andregasser/swisscom-myai-desk-lamp/output/multicolor_v4/print/04_base_P1S.3mf

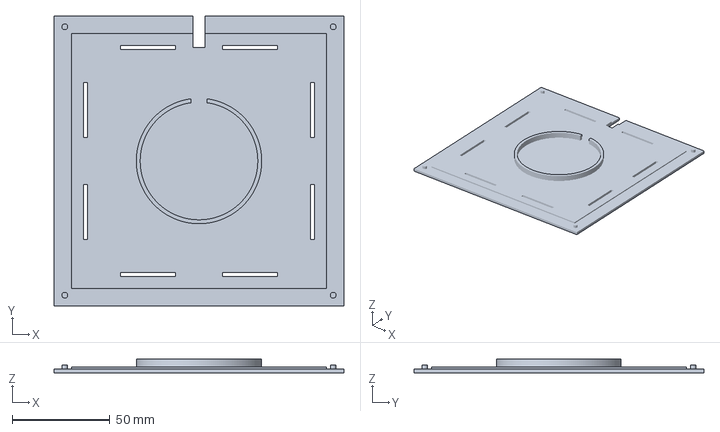
[picture p23: CAD file, 2026-09-30]
output/multicolor_v4/print/04_base_P1S.3mf
148.0 x 148.0 x 6.98 mm
