andregasser/swisscom-myai-desk-lamp/output/multicolor_v4/print/07_fit_P1S.3mf

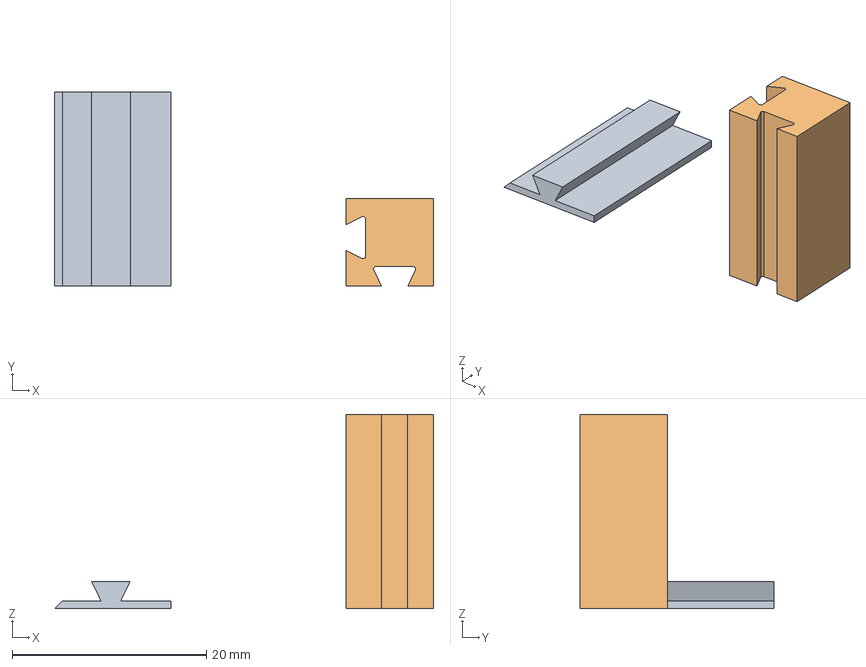
[picture p24: CAD file, 2026-09-30]
output/multicolor_v4/print/07_fit_P1S.3mf
39.0 x 20.0 x 20.0 mm
07_fit_panel
07_fit_corner
