andregasser/swisscom-myai-desk-lamp/output/multicolor_v4/stl/07_fit_corner.stl

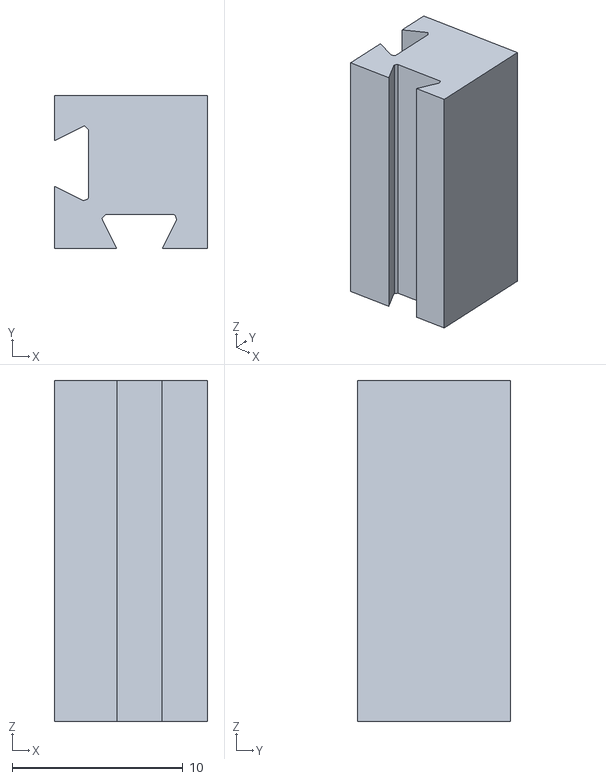
[picture p25: CAD file, 2026-09-30]
output/multicolor_v4/stl/07_fit_corner.stl
9.00 x 9.00 x 20.0
