andregasser/swisscom-myai-desk-lamp/output/stl/01f_joint_socket.stl

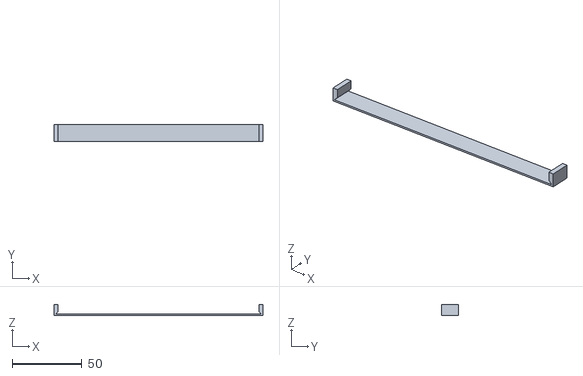
[picture p26: CAD file, 2026-09-28]
output/stl/01f_joint_socket.stl
150.0 x 12.0 x 8.00
