andregasser/swisscom-myai-desk-lamp/output/stl/01e_led_fit.stl

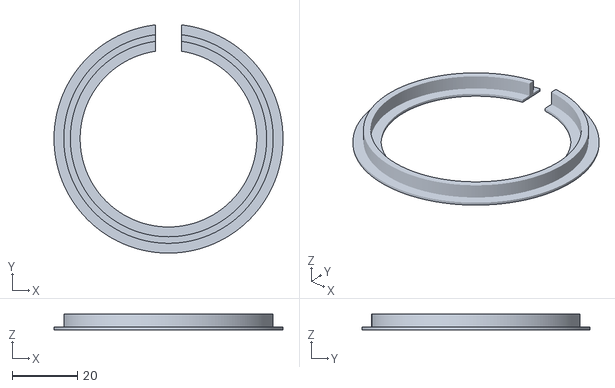
[picture p27: CAD file, 2026-09-28]
output/stl/01e_led_fit.stl
70.0 x 69.8 x 4.78
