andregasser/swisscom-myai-desk-lamp/output/stl/01g_joint_rail.stl

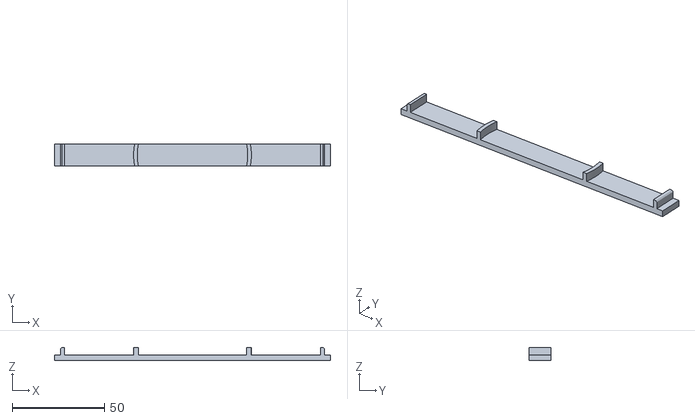
[picture p28: CAD file, 2026-09-28]
output/stl/01g_joint_rail.stl
150.0 x 12.0 x 7.00
