andregasser/swisscom-myai-desk-lamp/output/multicolor_v4/stl/02_panel_1_Weiss.stl

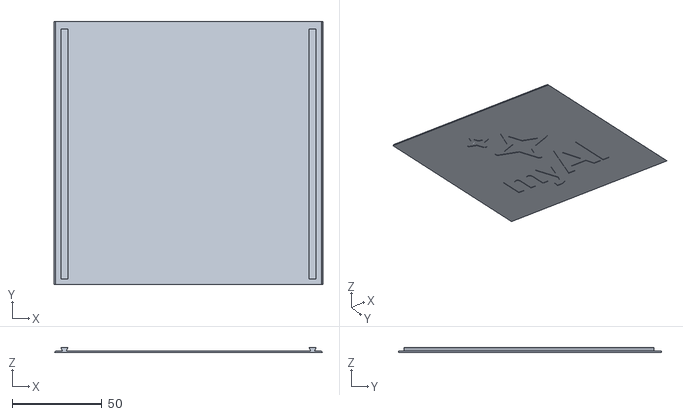
[picture p29: CAD file, 2026-09-30]
output/multicolor_v4/stl/02_panel_1_Weiss.stl
149.6 x 146.0 x 2.80
