andregasser/swisscom-myai-desk-lamp/output/stl/01d_light_1.2mm.stl

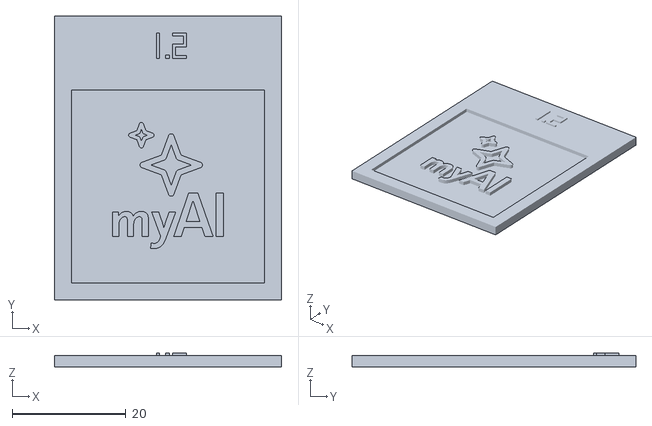
[picture p30: CAD file, 2026-09-28]
output/stl/01d_light_1.2mm.stl
40.0 x 50.0 x 2.38
