andregasser/swisscom-myai-desk-lamp/output/multicolor_v4/stl/02_panel_2_Blau.stl

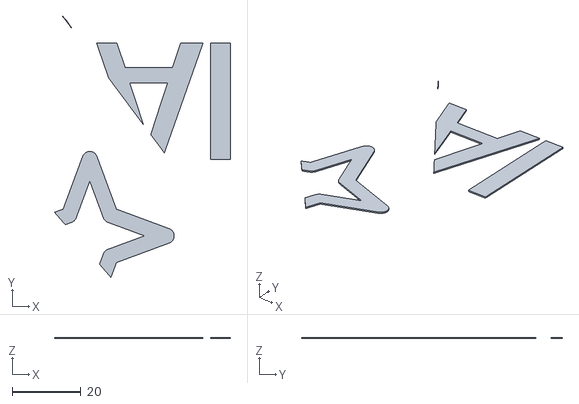
[picture p31: CAD file, 2026-09-30]
output/multicolor_v4/stl/02_panel_2_Blau.stl
51.1 x 75.8 x 0.4
