andregasser/swisscom-myai-desk-lamp/output/preview/assembled.png

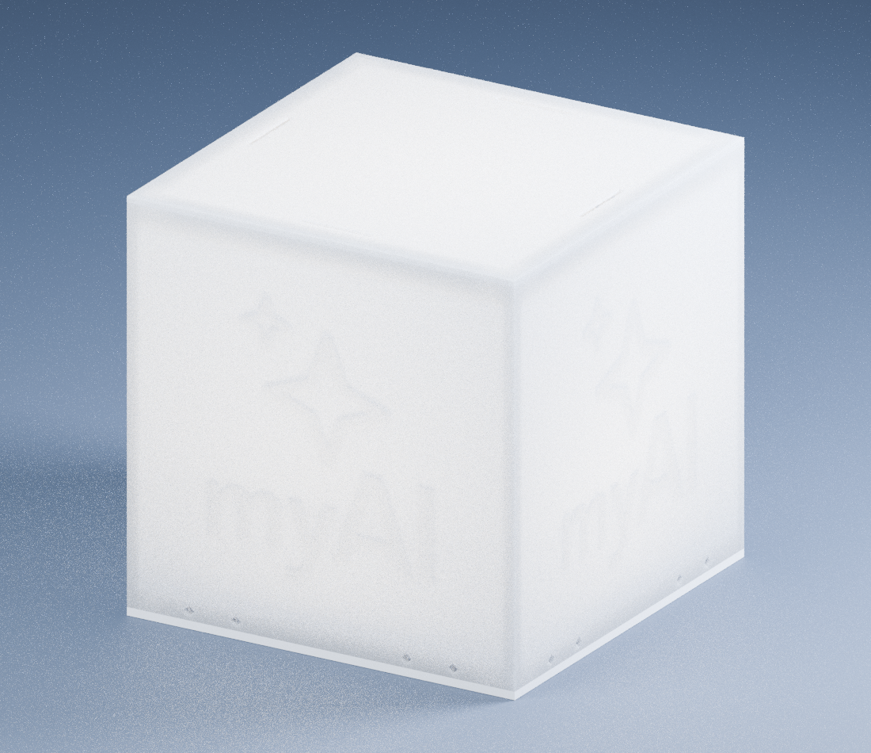
output/preview/assembled.png
